mdl29/panobus/website/img/anime.gif

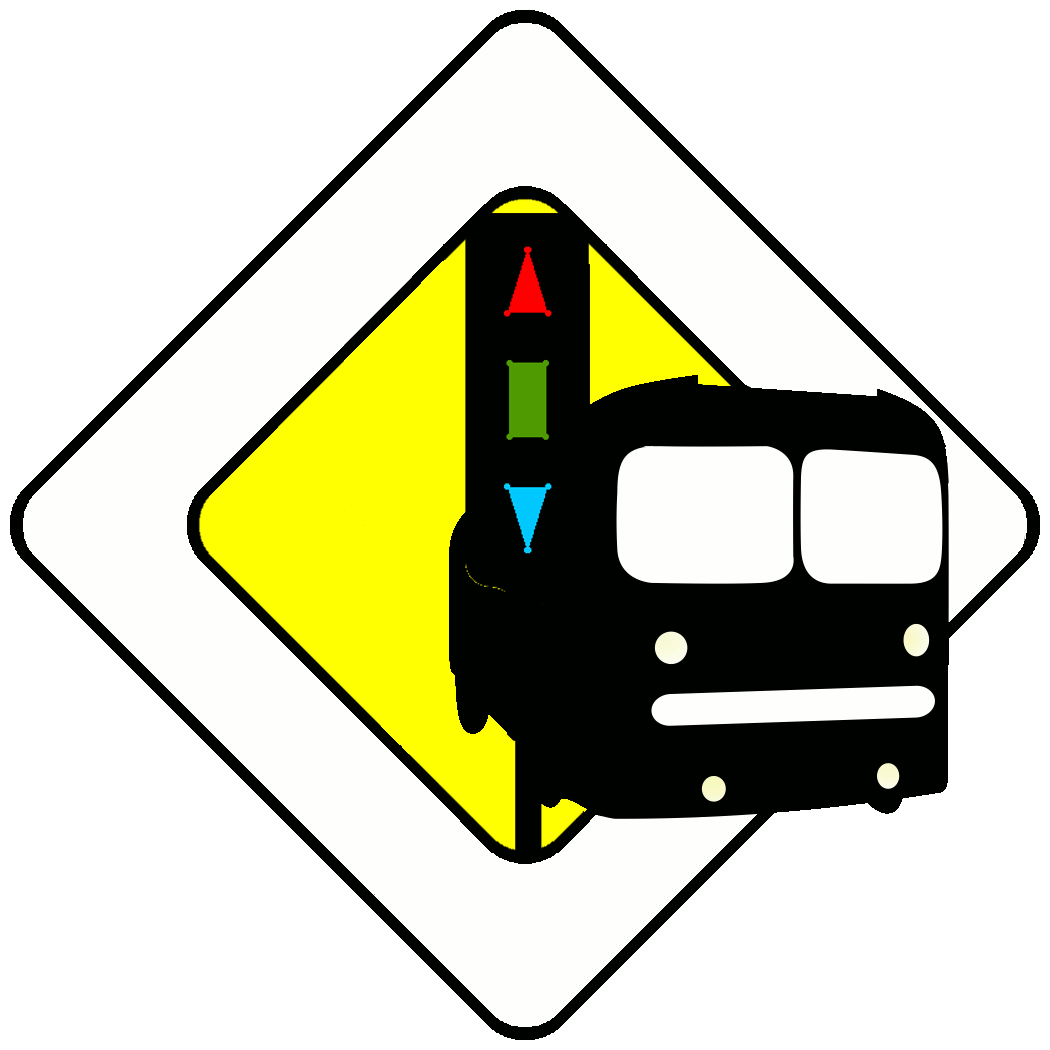
website/img/anime.gif
