mdl29/panobus/website/img/bg3c-light.jpg

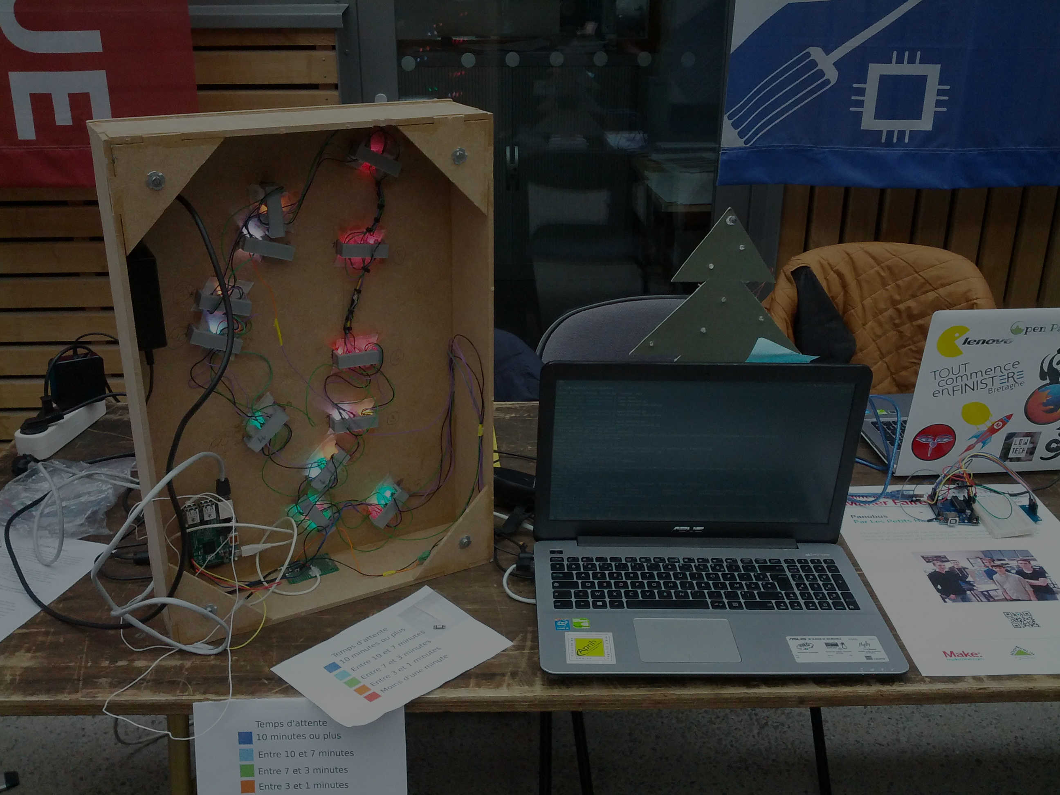
website/img/bg3c-light.jpg
