mdl29/panobus/website/img/bg4c-light.jpg

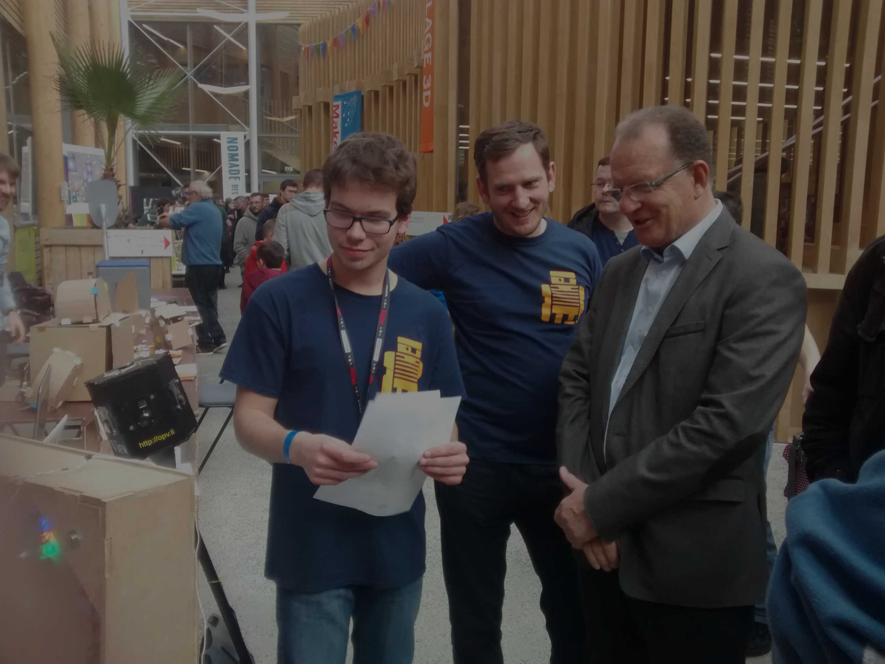
website/img/bg4c-light.jpg
