mdl29/panobus/website/img/bg5c-light.jpg

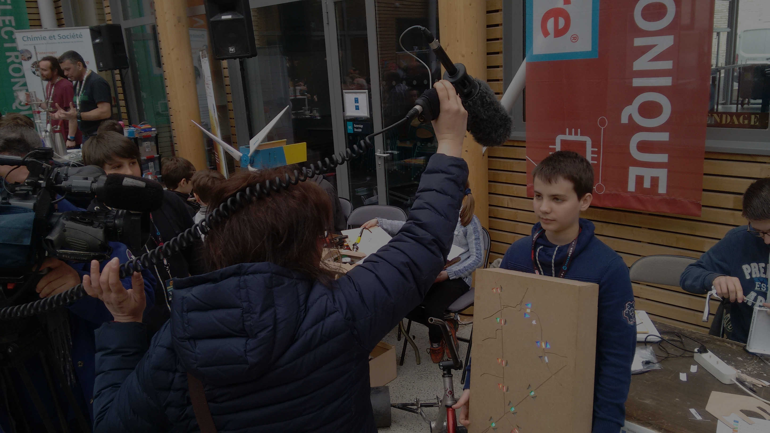
website/img/bg5c-light.jpg
