mdl29/panobus/website/img/brest.png

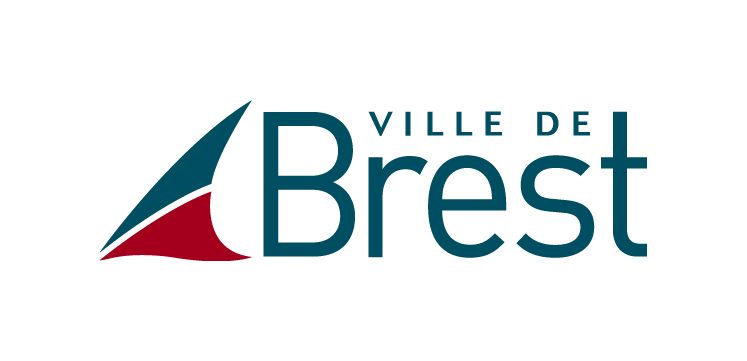
website/img/brest.png
