mdl29/panobus/website/img/panobus.png

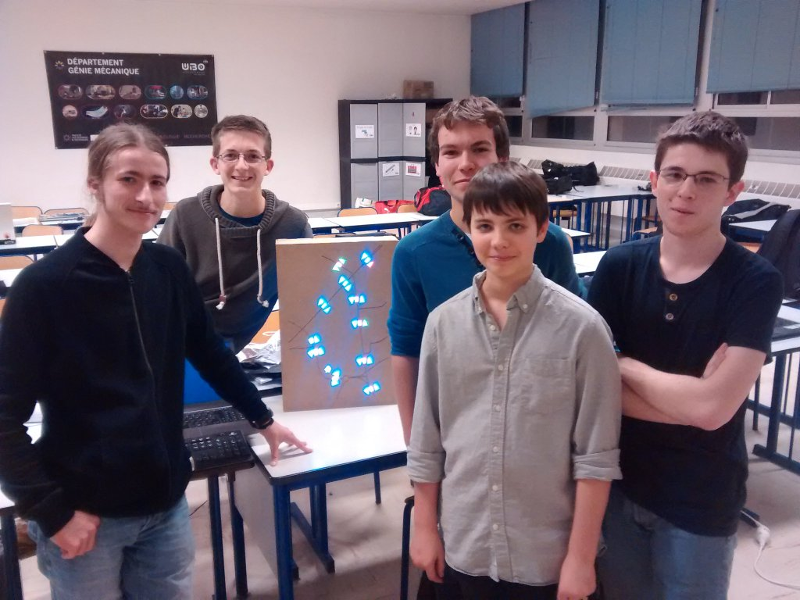
website/img/panobus.png
